robertfoss/esp8266_apa102_bulb/hardware/led_bulb.sch

## KiCad design hardware/led_bulb.sch (2016-10-09)

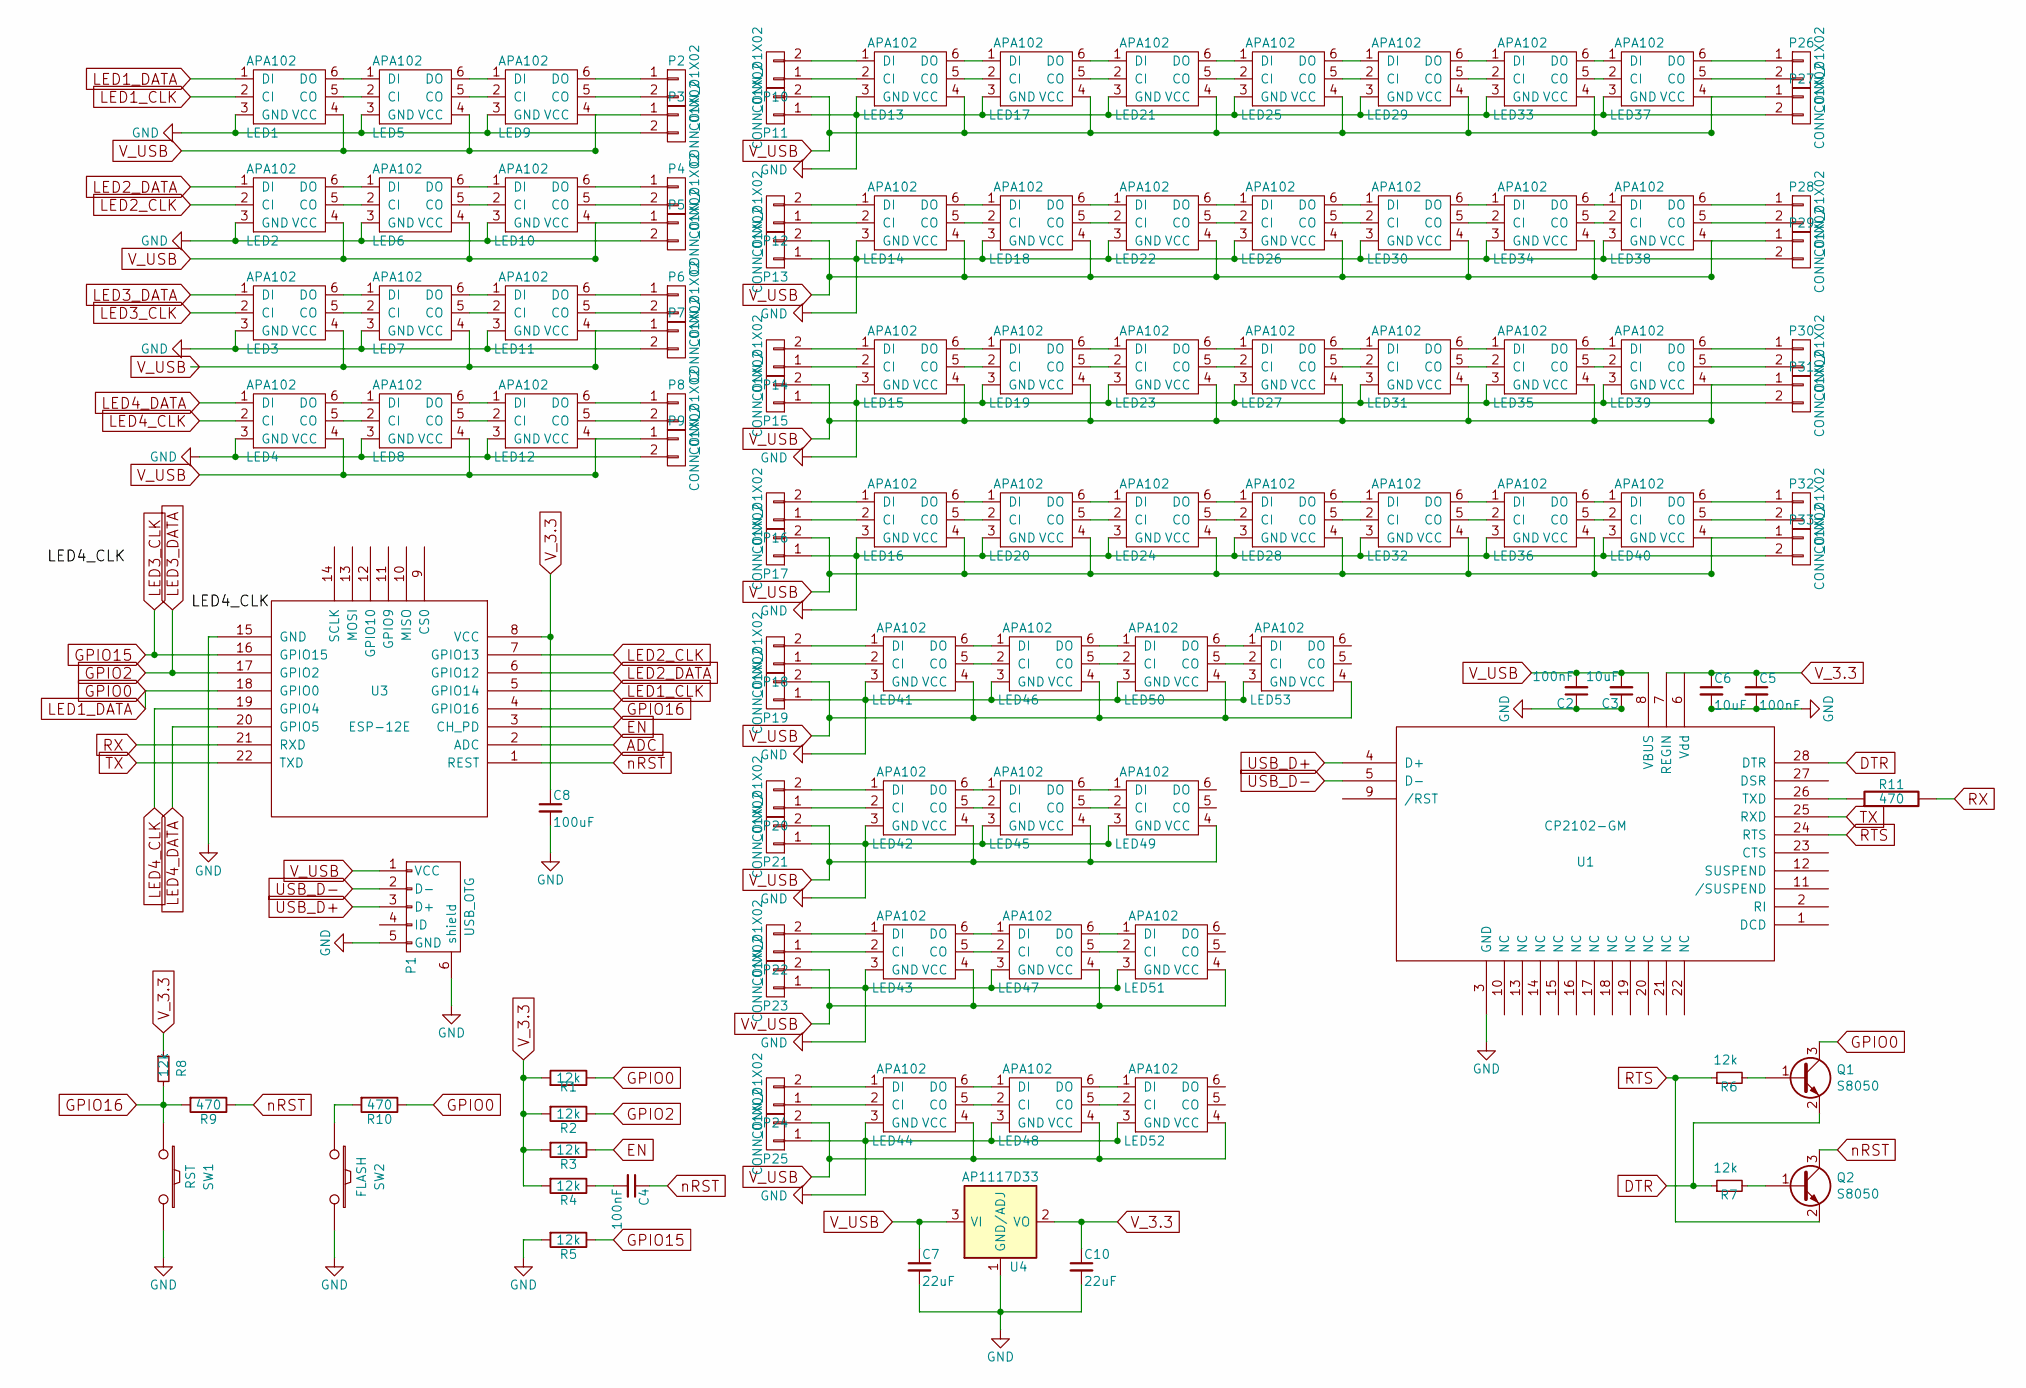
[picture p6: schematic led_bulb.sch]

Parts:
C2, C4, C5: 100nF; C_0603
C3, C6: 10uF; C_0603
C7, C10: 22uF; C_0805
C8: 100uF; C_0805
LED1, LED2, LED3, LED4, LED5, LED6, LED7, LED8, LED9, LED10, LED11, LED12, LED13, LED14, LED15, LED16, LED17, LED18, LED19, LED20, LED21, LED22, LED23, LED24, LED25, LED26, LED27, LED28, LED29, LED30, LED31, LED32, LED33, LED34, LED35, LED36, LED37, LED38, LED39, LED40, LED41, LED42, LED43, LED44, LED45, LED46, LED47, LED48, LED49, LED50, LED51, LED52, LED53: APA102
P1: USB_OTG; USB_Micro-B
P2, P3, P4, P5, P6, P7, P8, P9, P10, P11, P12, P13, P14, P15, P16, P17, P18, P19, P20, P21, P22, P23, P24, P25, P26, P27, P28, P29, P30, P31, P32, P33: CONN_01X02; CONN_2.54mm_1x2_no-outline
Q1, Q2: S8050
R1, R2, R3, R4, R5, R6, R7, R8: 12k; R_0603
R9, R10, R11: 470; R_0603
SW1: RST; B3F-1050
SW2: FLASH; B3F-1050
U1: CP2102-GM; QFN-28-1EP_5x5mm_Pitch0.5mm
U3: ESP-12E
U4: AP1117D33; SOT-223

Connections:
ADC: U3.2 (ADC)
DTR: Q1.2 (E), R7.1, U1.28 (DTR)
EN: R3.1, U3.3 (CH_PD)
GND: C2.1, C3.1, C5.2, C6.2, C7.2, C8.2, C10.2, LED1.3 (GND), LED2.3 (GND), LED3.3 (GND), LED4.3 (GND), LED5.3 (GND), LED6.3 (GND), LED7.3 (GND), LED8.3 (GND), LED9.3 (GND), LED10.3 (GND), LED11.3 (GND), LED12.3 (GND), LED13.3 (GND), LED14.3 (GND), LED15.3 (GND), LED16.3 (GND), LED17.3 (GND), LED18.3 (GND), LED19.3 (GND), LED20.3 (GND), LED21.3 (GND), LED22.3 (GND), LED23.3 (GND), LED24.3 (GND), LED25.3 (GND), LED26.3 (GND), LED27.3 (GND), LED28.3 (GND), LED29.3 (GND), LED30.3 (GND), LED31.3 (GND), LED32.3 (GND), LED33.3 (GND), LED34.3 (GND), LED35.3 (GND), LED36.3 (GND), LED37.3 (GND), LED38.3 (GND), LED39.3 (GND), LED40.3 (GND), LED41.3 (GND), LED42.3 (GND), LED43.3 (GND), LED44.3 (GND), LED45.3 (GND), LED46.3 (GND), LED47.3 (GND), LED48.3 (GND), LED49.3 (GND), LED50.3 (GND), LED51.3 (GND), LED52.3 (GND), LED53.3 (GND), P1.5 (GND), P1.6 (shield), P3.2, P5.2, P7.2, P9.2, P11.1, P13.1, P15.1, P17.1, P19.1, P21.1, P23.1, P25.1, P27.2, P29.2, P31.2, P33.2, R5.2, SW1.2, SW2.2, U1.3 (GND), U3.15 (GND), U4.1 (GND/ADJ)
GPIO0: LED1.1 (DI), Q1.3 (C), R1.1, R10.1, U3.18 (GPIO0)
GPIO2: LED3.1 (DI), R2.1, U3.17 (GPIO2)
GPIO15: LED3.2 (CI), R5.1, U3.16 (GPIO15)
GPIO16: R8.2, R9.2, SW1.1, U3.4 (GPIO16)
LED1_CLK: LED1.2 (CI), U3.5 (GPIO14)
LED2_CLK: LED2.2 (CI), U3.7 (GPIO13)
LED2_DATA: LED2.1 (DI), U3.6 (GPIO12)
LED4_CLK: LED4.2 (CI), U3.19 (GPIO4)
LED4_DATA: LED4.1 (DI), U3.20 (GPIO5)
unnamed: C4.2, R4.1
unnamed: LED1.5 (CO), LED5.2 (CI)
unnamed: LED1.6 (DO), LED5.1 (DI)
unnamed: LED2.5 (CO), LED6.2 (CI)
unnamed: LED2.6 (DO), LED6.1 (DI)
unnamed: LED3.5 (CO), LED7.2 (CI)
unnamed: LED3.6 (DO), LED7.1 (DI)
unnamed: LED4.5 (CO), LED8.2 (CI)
unnamed: LED4.6 (DO), LED8.1 (DI)
unnamed: LED5.5 (CO), LED9.2 (CI)
unnamed: LED5.6 (DO), LED9.1 (DI)
unnamed: LED9.5 (CO), P2.2
unnamed: LED9.6 (DO), P2.1
unnamed: LED6.6 (DO), LED10.1 (DI)
unnamed: LED6.5 (CO), LED10.2 (CI)
unnamed: LED10.5 (CO), P4.2
unnamed: LED10.6 (DO), P4.1
unnamed: LED7.6 (DO), LED11.1 (DI)
unnamed: LED7.5 (CO), LED11.2 (CI)
unnamed: LED11.5 (CO), P6.2
unnamed: LED11.6 (DO), P6.1
unnamed: LED8.6 (DO), LED12.1 (DI)
unnamed: LED8.5 (CO), LED12.2 (CI)
unnamed: LED12.5 (CO), P8.2
unnamed: LED12.6 (DO), P8.1
unnamed: LED13.1 (DI), P10.2
unnamed: LED13.2 (CI), P10.1
unnamed: LED13.5 (CO), LED17.2 (CI)
unnamed: LED13.6 (DO), LED17.1 (DI)
unnamed: LED14.1 (DI), P12.2
unnamed: LED14.2 (CI), P12.1
unnamed: LED14.5 (CO), LED18.2 (CI)
unnamed: LED14.6 (DO), LED18.1 (DI)
unnamed: LED15.1 (DI), P14.2
unnamed: LED15.2 (CI), P14.1
unnamed: LED15.5 (CO), LED19.2 (CI)
unnamed: LED15.6 (DO), LED19.1 (DI)
unnamed: LED16.1 (DI), P16.2
unnamed: LED16.2 (CI), P16.1
unnamed: LED16.5 (CO), LED20.2 (CI)
unnamed: LED16.6 (DO), LED20.1 (DI)
unnamed: LED17.5 (CO), LED21.2 (CI)
unnamed: LED17.6 (DO), LED21.1 (DI)
unnamed: LED18.5 (CO), LED22.2 (CI)
unnamed: LED18.6 (DO), LED22.1 (DI)
unnamed: LED19.5 (CO), LED23.2 (CI)
unnamed: LED19.6 (DO), LED23.1 (DI)
unnamed: LED20.5 (CO), LED24.2 (CI)
unnamed: LED20.6 (DO), LED24.1 (DI)
unnamed: LED21.5 (CO), LED25.2 (CI)
unnamed: LED21.6 (DO), LED25.1 (DI)
unnamed: LED22.5 (CO), LED26.2 (CI)
unnamed: LED22.6 (DO), LED26.1 (DI)
unnamed: LED23.5 (CO), LED27.2 (CI)
unnamed: LED23.6 (DO), LED27.1 (DI)
unnamed: LED24.5 (CO), LED28.2 (CI)
unnamed: LED24.6 (DO), LED28.1 (DI)
unnamed: LED25.5 (CO), LED29.2 (CI)
unnamed: LED25.6 (DO), LED29.1 (DI)
unnamed: LED26.5 (CO), LED30.2 (CI)
unnamed: LED26.6 (DO), LED30.1 (DI)
unnamed: LED27.5 (CO), LED31.2 (CI)
unnamed: LED27.6 (DO), LED31.1 (DI)
unnamed: LED28.5 (CO), LED32.2 (CI)
unnamed: LED28.6 (DO), LED32.1 (DI)
unnamed: LED29.5 (CO), LED33.2 (CI)
unnamed: LED29.6 (DO), LED33.1 (DI)
unnamed: LED30.5 (CO), LED34.2 (CI)
unnamed: LED30.6 (DO), LED34.1 (DI)
unnamed: LED31.5 (CO), LED35.2 (CI)
unnamed: LED31.6 (DO), LED35.1 (DI)
unnamed: LED32.5 (CO), LED36.2 (CI)
unnamed: LED32.6 (DO), LED36.1 (DI)
unnamed: LED33.5 (CO), LED37.2 (CI)
unnamed: LED33.6 (DO), LED37.1 (DI)
unnamed: LED34.5 (CO), LED38.2 (CI)
unnamed: LED34.6 (DO), LED38.1 (DI)
unnamed: LED35.5 (CO), LED39.2 (CI)
unnamed: LED35.6 (DO), LED39.1 (DI)
unnamed: LED36.5 (CO), LED40.2 (CI)
unnamed: LED36.6 (DO), LED40.1 (DI)
unnamed: LED37.5 (CO), P26.2
unnamed: LED37.6 (DO), P26.1
unnamed: LED38.5 (CO), P28.2
unnamed: LED38.6 (DO), P28.1
unnamed: LED39.5 (CO), P30.2
unnamed: LED39.6 (DO), P30.1
unnamed: LED40.5 (CO), P32.2
unnamed: LED40.6 (DO), P32.1
unnamed: LED41.1 (DI), P18.2
unnamed: LED41.2 (CI), P18.1
unnamed: LED41.5 (CO), LED46.2 (CI)
unnamed: LED41.6 (DO), LED46.1 (DI)
unnamed: LED42.1 (DI), P20.2
unnamed: LED42.2 (CI), P20.1
unnamed: LED42.5 (CO), LED45.2 (CI)
unnamed: LED42.6 (DO), LED45.1 (DI)
unnamed: LED43.1 (DI), P22.2
unnamed: LED43.2 (CI), P22.1
unnamed: LED43.5 (CO), LED47.2 (CI)
unnamed: LED43.6 (DO), LED47.1 (DI)
unnamed: LED44.1 (DI), P24.2
unnamed: LED44.2 (CI), P24.1
unnamed: LED44.5 (CO), LED48.2 (CI)
unnamed: LED44.6 (DO), LED48.1 (DI)
unnamed: LED45.5 (CO), LED49.2 (CI)
unnamed: LED45.6 (DO), LED49.1 (DI)
unnamed: LED46.5 (CO), LED50.2 (CI)
unnamed: LED46.6 (DO), LED50.1 (DI)
unnamed: LED47.5 (CO), LED51.2 (CI)
unnamed: LED47.6 (DO), LED51.1 (DI)
unnamed: LED48.5 (CO), LED52.2 (CI)
unnamed: LED48.6 (DO), LED52.1 (DI)
unnamed: LED50.5 (CO), LED53.2 (CI)
unnamed: LED50.6 (DO), LED53.1 (DI)
unnamed: Q1.1 (B), R6.2
unnamed: Q2.1 (B), R7.2
unnamed: R10.2, SW2.1
unnamed: R11.1, U1.26 (TXD)
RTS: Q2.2 (E), R6.1, U1.24 (RTS)
RX: R11.2, U3.21 (RXD)
TX: U1.25 (RXD), U3.22 (TXD)
USB_D+: P1.3 (D+), U1.4 (D+)
USB_D-: P1.2 (D-), U1.5 (D-)
V_3.3: C5.1, C6.1, C8.1, C10.1, R1.2, R2.2, R3.2, R4.2, R8.1, U1.7 (REGIN), U3.8 (VCC), U4.2 (VO)
V_USB: C2.2, C3.2, C7.1, LED1.4 (VCC), LED2.4 (VCC), LED3.4 (VCC), LED4.4 (VCC), LED5.4 (VCC), LED6.4 (VCC), LED7.4 (VCC), LED8.4 (VCC), LED9.4 (VCC), LED10.4 (VCC), LED11.4 (VCC), LED12.4 (VCC), LED13.4 (VCC), LED14.4 (VCC), LED15.4 (VCC), LED16.4 (VCC), LED17.4 (VCC), LED18.4 (VCC), LED19.4 (VCC), LED20.4 (VCC), LED21.4 (VCC), LED22.4 (VCC), LED23.4 (VCC), LED24.4 (VCC), LED25.4 (VCC), LED26.4 (VCC), LED27.4 (VCC), LED28.4 (VCC), LED29.4 (VCC), LED30.4 (VCC), LED31.4 (VCC), LED32.4 (VCC), LED33.4 (VCC), LED34.4 (VCC), LED35.4 (VCC), LED36.4 (VCC), LED37.4 (VCC), LED38.4 (VCC), LED39.4 (VCC), LED40.4 (VCC), LED41.4 (VCC), LED42.4 (VCC), LED44.4 (VCC), LED45.4 (VCC), LED46.4 (VCC), LED48.4 (VCC), LED49.4 (VCC), LED50.4 (VCC), LED52.4 (VCC), LED53.4 (VCC), P1.1 (VCC), P3.1, P5.1, P7.1, P9.1, P11.2, P13.2, P15.2, P17.2, P19.2, P21.2, P25.2, P27.1, P29.1, P31.1, P33.1, U1.8 (VBUS), U4.3 (VI)
Vv_USB: LED43.4 (VCC), LED47.4 (VCC), LED51.4 (VCC), P23.2
nRST: C4.1, Q2.3 (C), R9.1, U3.1 (REST)
